Smart-Ingredient-Scale/schematics/docs/pcb-soldermask-blue1.png

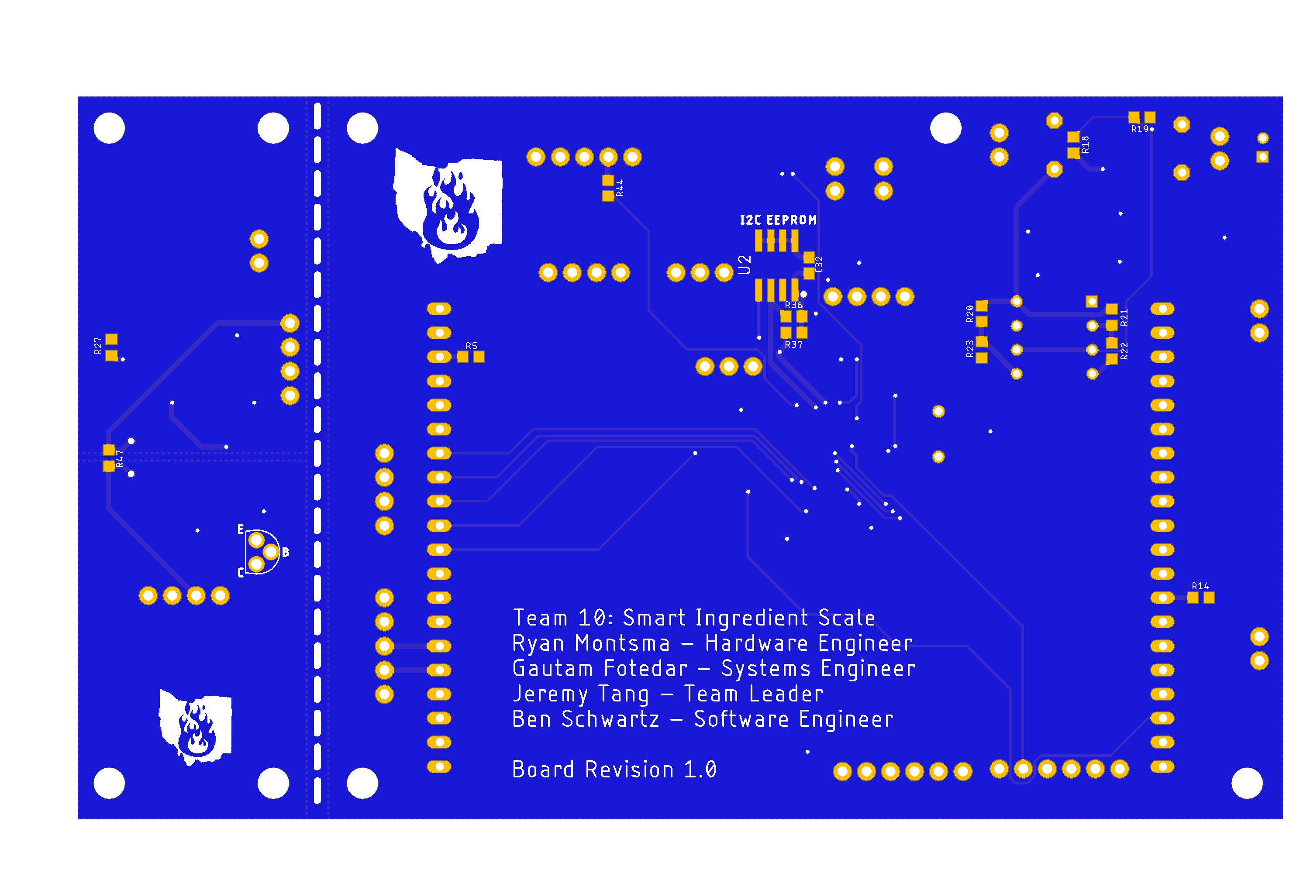
docs/pcb-soldermask-blue1.png
