Smart-Ingredient-Scale/schematics/docs/pcb-soldermask-blue.png

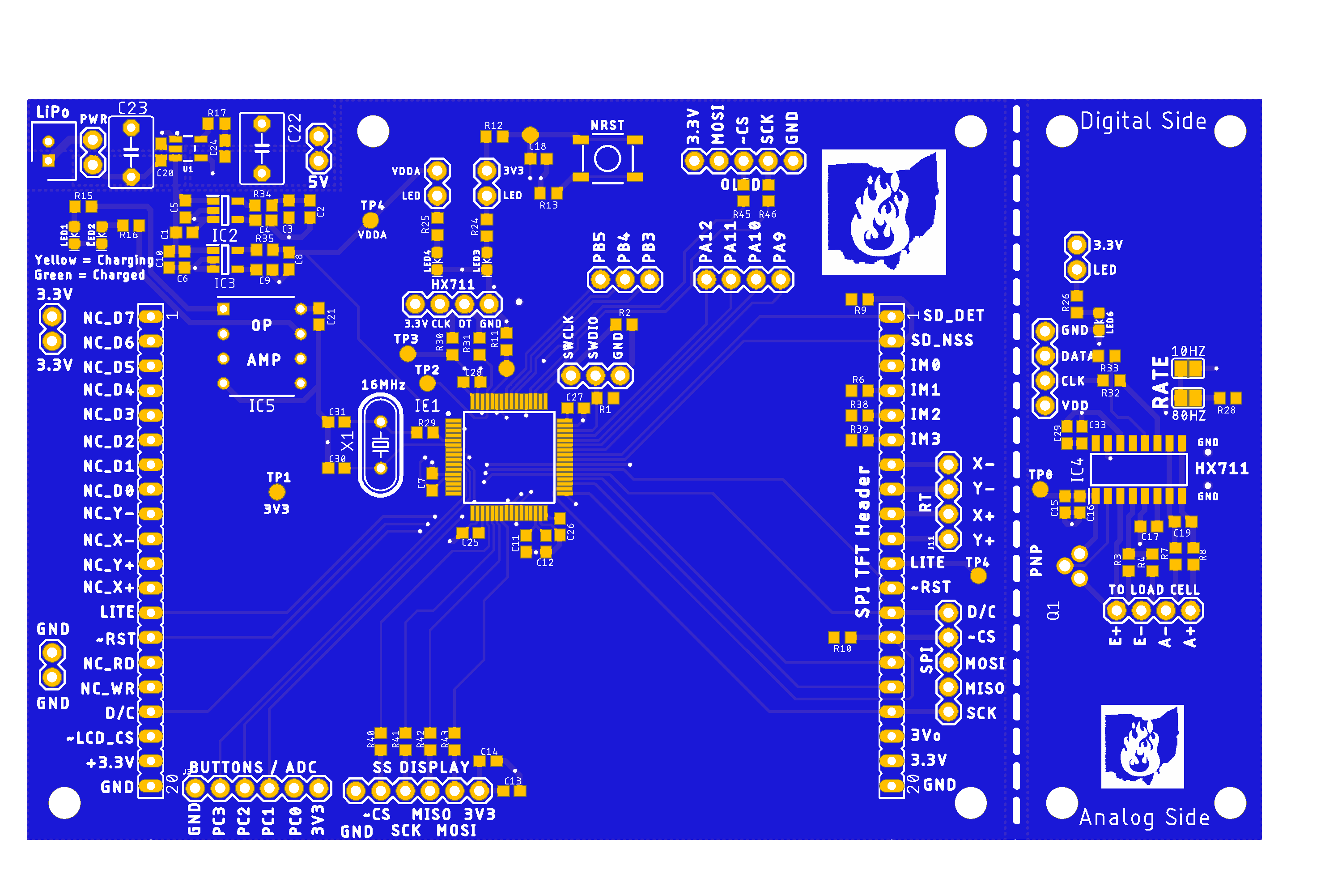
docs/pcb-soldermask-blue.png
